hansj66/NixieKit/enclosures/alternative1/STEP/base_bottom.step

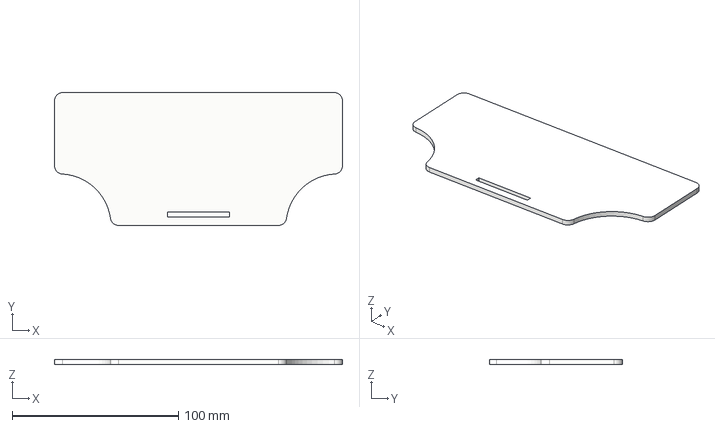
[picture p20: CAD file, 2019-12-27]
enclosures/alternative1/STEP/base_bottom.step
173.5 x 80.0 x 3.00 mm
