hansj66/NixieKit/enclosures/alternative2/STEP/PCB_Bracket2.step

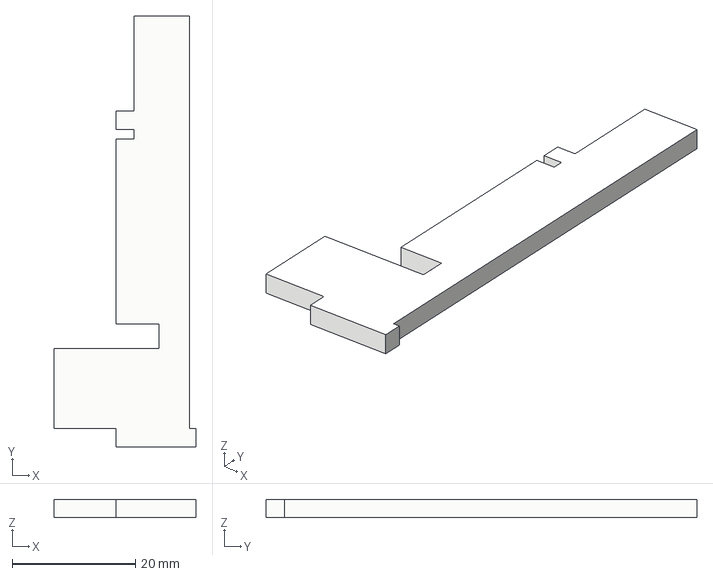
[picture p21: CAD file, 2021-09-23]
enclosures/alternative2/STEP/PCB_Bracket2.step
23.0 x 70.0 x 3.00 mm
