hansj66/NixieKit/enclosures/alternative2/STEP/Wood_Right.step

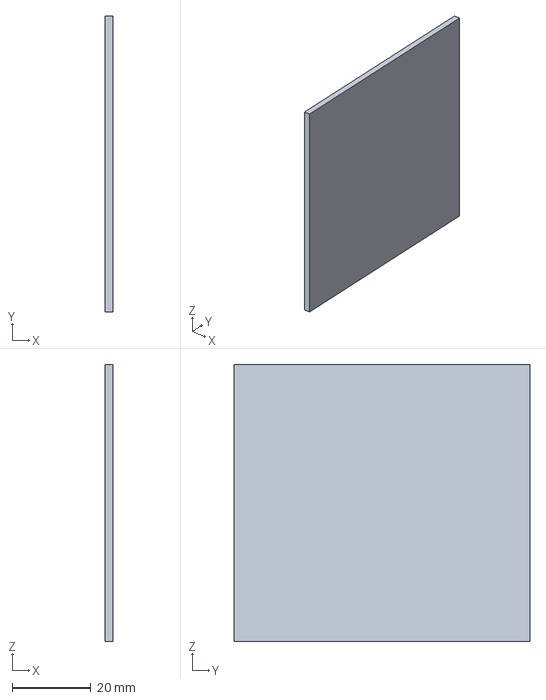
[picture p22: CAD file, 2021-09-23]
enclosures/alternative2/STEP/Wood_Right.step
2.00 x 75.0 x 70.3 mm
