hansj66/NixieKit/enclosures/alternative2/STEP/Front.step

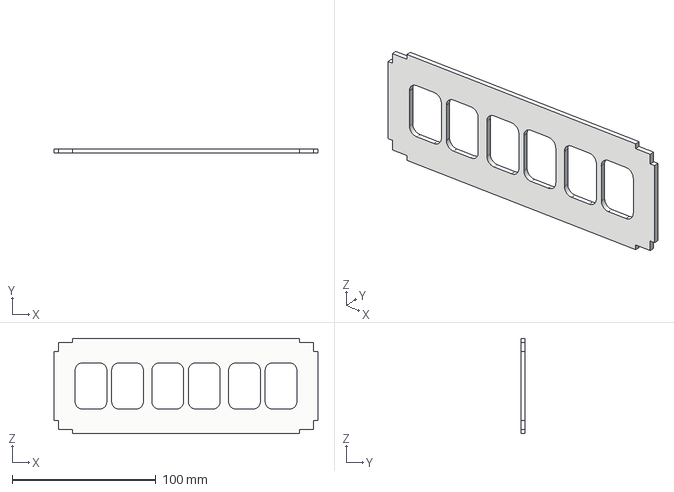
[picture p23: CAD file, 2021-09-23]
enclosures/alternative2/STEP/Front.step
183.5 x 3.00 x 66.3 mm
