hansj66/NixieKit/enclosures/alternative2/STEP/PCB.step

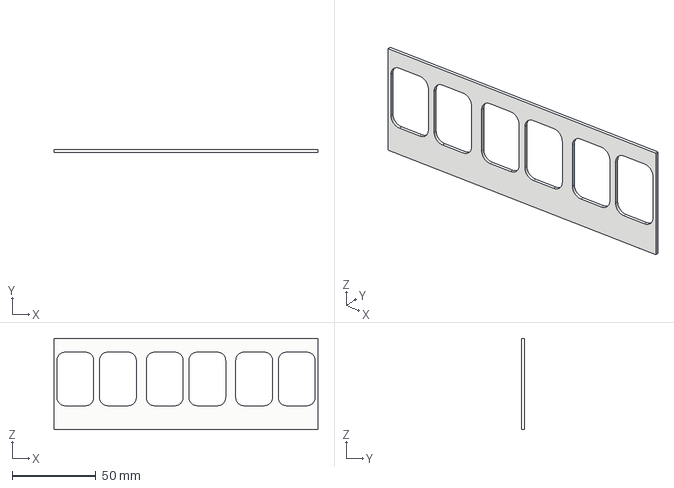
[picture p25: CAD file, 2021-09-23]
enclosures/alternative2/STEP/PCB.step
157.5 x 1.60 x 54.3 mm
