hansj66/NixieKit/enclosures/alternative2/STEP/Wood_Front.step

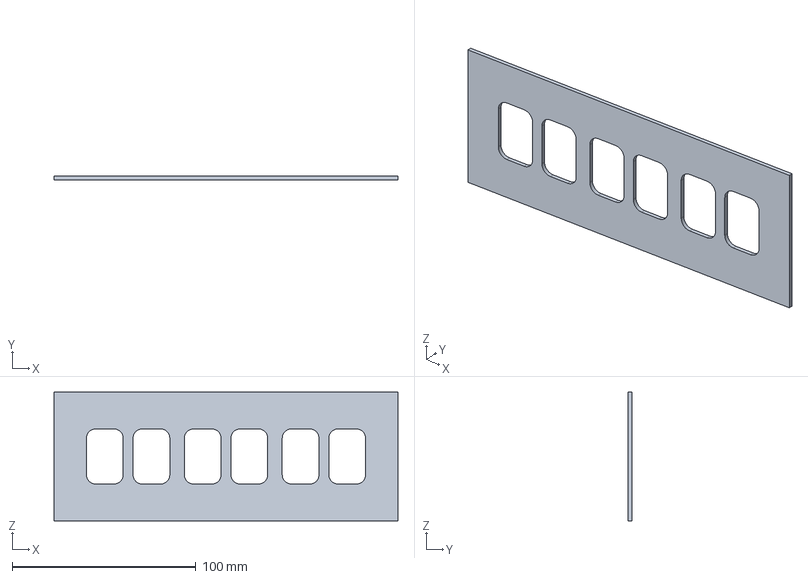
[picture p26: CAD file, 2021-09-23]
enclosures/alternative2/STEP/Wood_Front.step
187.5 x 2.00 x 70.3 mm
