hansj66/NixieKit/enclosures/alternative2/STEP/Backplane.step

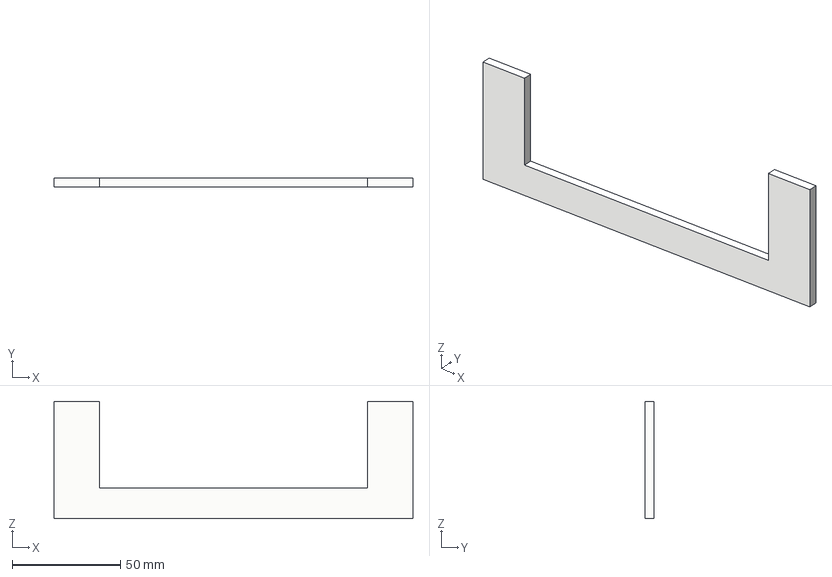
[picture p27: CAD file, 2021-09-23]
enclosures/alternative2/STEP/Backplane.step
165.5 x 4.00 x 54.0 mm
